mircoick/ANS-VCO-Projekt-2026/sim/Wien-VCO-aufbau.asc

C1: cap; {C}
C2: cap; {C}
C3: cap; 2nF
C4: cap; 100nF
C5: cap; 100nF
D1: diode; 1N6263
J1: njf; J113
R1: res; {R}
R2: res; {R}
R3: res; 2k55
R4: res; 1K2
R5: res; 20K
R7: res; 1K
R8: res; 5K
U2: LT1363
VCC+: voltage; 10V
VCC-: voltage; -10V
Named nets: 0, VCC+, VCC-, ve, va, v2
* Includes
.include ../kicad/spicelibs/MAX4104.lib
.include ../kicad/spicelibs/elk.lib
 
* Parameter
.param R=3k3
.param C=15pF
 
 
* Initial Condition
.nodeset V(va)=1
 
* Models
.model 1N6263 D(Is=1.82u Rs=2.8 N=1.7 Cjo=2.65p M=0.333 tt=1.44n BV=60 Ibv=200n)
 
* Analysemethode
.tran 1n 200u
 
.meas tran t1 trig V(va) val=0 rise=1
.meas tran t2 trig V(va) val=0 rise=11
.meas TRAN frequenz PARAM abs(10/(t2-t1))
