mircoick/ANS-VCO-Projekt-2026/sim/Wien-VCO.asc

C1: cap; {C}
C2: cap; {C}
C3: cap; 2nF
C4: cap; 100nF
C5: cap; 100nF
D1: diode; 1N6263
D2: varactor; BB535/SIE
D3: varactor; BB535/SIE
D4: varactor; BB535/SIE
D5: varactor; BB535/SIE
J1: njf; J113
R1: res; {R}
R2: res; {R}
R3: res; 2k32
R4: res; 1K2
R5: res; 20K
R6: res; 100K
R7: res; 1K
R8: res; 5K
R9: res; 100K
R10: res; 10K
R11: res; 75K
R12: res; 50K
U1: opamp2; MAX4104
U2: opamp2; TL082
V1: voltage; 0V
VCC+: voltage; 10V
VCC-: voltage; -10V
Named nets: 0, VCC+, VCC-, ve, va, v2, Vstr, Vin
* Includes
.include ../kicad/spicelibs/MAX4104.lib
.include ../kicad/spicelibs/elk.lib
 
* Parameter
.param R=3K275
.param C=2.7pF
 
* Step-Parameter
.step V1 0V 1V 0.1V
 
* Initial Condition
.nodeset V(va)=1
 
* Models
.model BB535/SIE D (IS=1.75E-15 N=1.043 RS=60E-3 XTI=3 EG=1.11 CJO=25.31E-12 M=1.064 VJ=3.022 FC=.5 BV=32 IBV=100E-9 TT=120E-9 )
.model 1N6263 D(Is=1.82u Rs=2.8 N=1.7 Cjo=2.65p M=0.333 tt=1.44n BV=60 Ibv=200n)
 
* Analysemethode
.tran 0 900u 800u
 
.meas tran t1 trig V(va) val=0 rise=1
.meas tran t2 trig V(va) val=0 rise=11
.meas TRAN frequenz PARAM abs(10/(t2-t1))
